Asystole-2/Thermo-Track/src/run_motion.py

import os
import time
from dotenv import load_dotenv, find_dotenv
from core.motion.motion_service import MotionService

load_dotenv(find_dotenv())


def main():
    try:
        pir_pin = int(os.getenv("PIR_PIN", "11"))
        buzzer_pin = int(os.getenv("BUZZER_PIN", "7"))
        service = MotionService(pir_pin=pir_pin, buzzer_pin=buzzer_pin)
        service.run()
    except RuntimeError as e:
        # Clean message on non-Pi machines
        print(str(e))

if __name__ == "__main__":
    main()
